fryefryefrye/Open-Source-RKS/OtherProject/clock/1.jpg

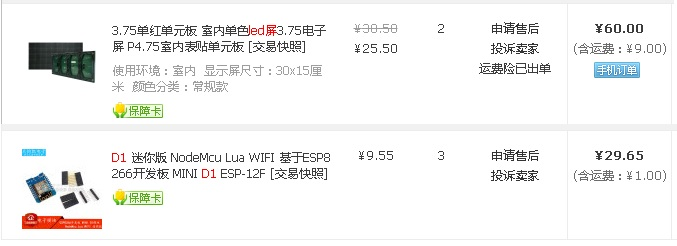
OtherProject/clock/1.jpg
