fryefryefrye/Open-Source-RKS/OtherProject/clock/2.jpg

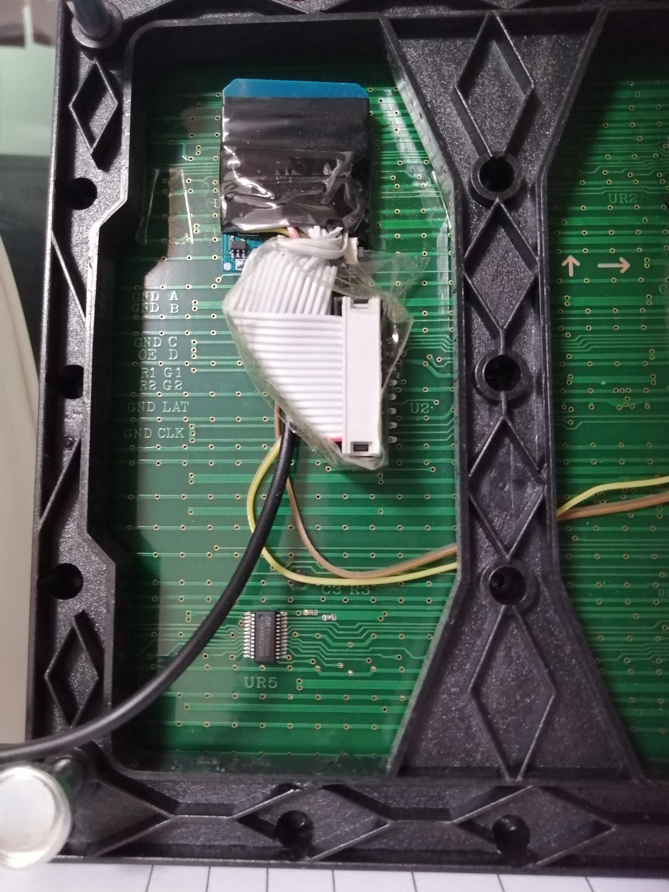
OtherProject/clock/2.jpg
