fryefryefrye/Open-Source-RKS/OtherProject/clock/3.jpg

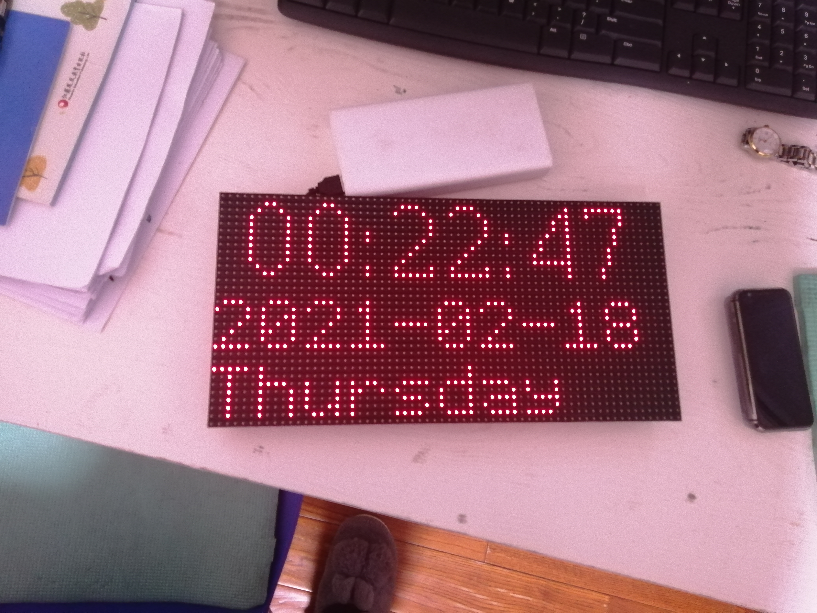
OtherProject/clock/3.jpg
