fryefryefrye/Open-Source-RKS/OtherProject/clock/4.jpg

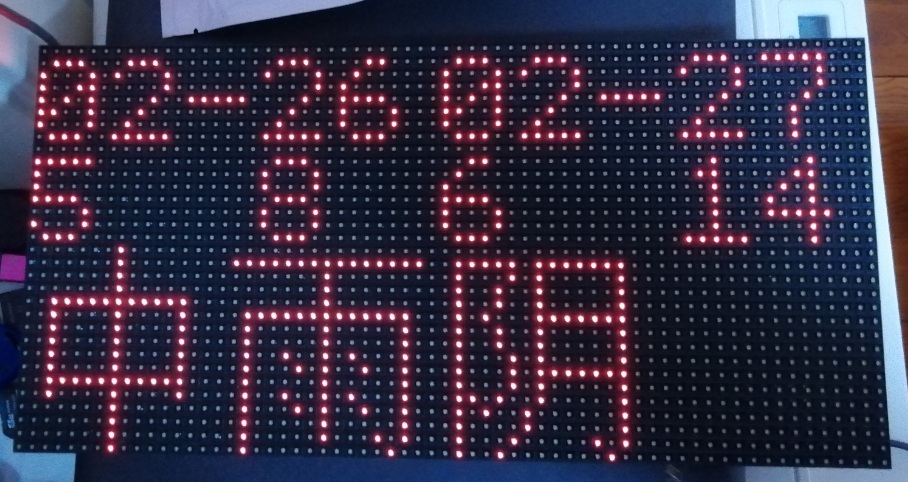
OtherProject/clock/4.jpg
