fryefryefrye/Open-Source-RKS/OtherProject/clock/IMG_20210221_115505.jpg

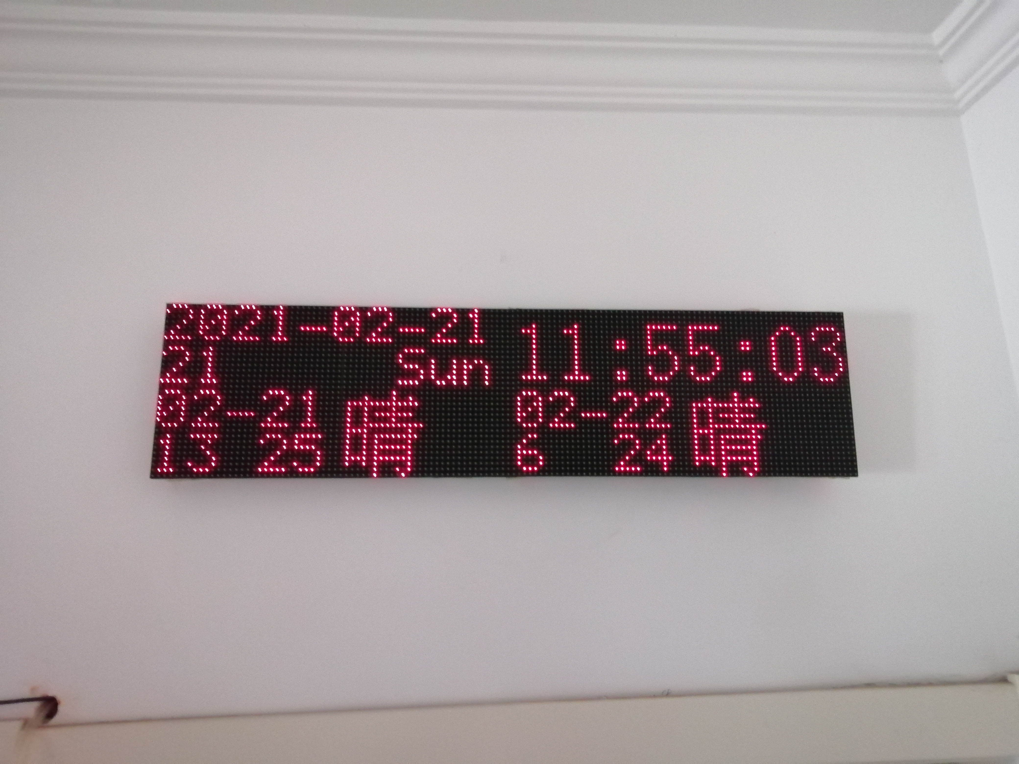
OtherProject/clock/IMG_20210221_115505.jpg
