fryefryefrye/Open-Source-RKS/OtherProject/HomeAutomation/1.jpg

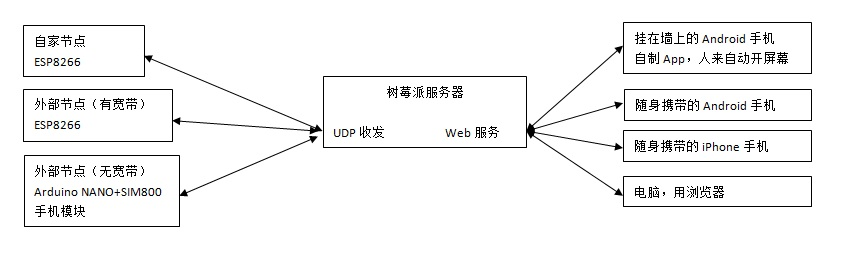
OtherProject/HomeAutomation/1.jpg
