fryefryefrye/Open-Source-RKS/OtherProject/HomeAutomation/2.jpg

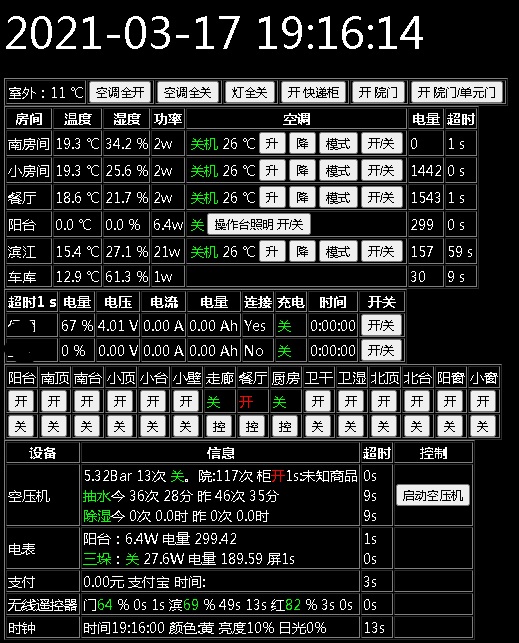
OtherProject/HomeAutomation/2.jpg
