fryefryefrye/Open-Source-RKS/Tag/ble/hal/nordic_common.h

/* Copyright (c) 2009 Nordic Semiconductor. All Rights Reserved.
 *
 * The information contained herein is confidential property of Nordic 
 * Semiconductor ASA.Terms and conditions of usage are described in detail 
 * in NORDIC SEMICONDUCTOR STANDARD SOFTWARE LICENSE AGREEMENT. 
 *
 * Licensees are granted free, non-transferable use of the information. NO
 * WARRENTY of ANY KIND is provided. This heading must NOT be removed from
 * the file.
 *              
 * $LastChangedRevision: 2513 $
 */

/** @file
 * @brief Common defines and macros for firmware developed by Nordic Semiconductor.
 *
 */

#ifndef NORDIC_COMMON_H__
#define NORDIC_COMMON_H__

/** Swaps the upper byte with the lower byte in a 16 bit variable */
//lint -emacro((572),SWAP) // Suppress warning 572 "Excessive shift value"
#define SWAP(x) ((((x)&0xFFU)<<8)|(((x)>>8)&0xFFU))

/** The upper 8 bits of a 16 bit value */
#define MSB(a) (((a) & 0xFF00U) >> 8)
/** The lower 8 bits (of a 16 bit value) */
#define LSB(a) (((a) & 0xFFU))

/** Leaves the minimum of the two arguments */
#define MIN(a, b) ((a) < (b) ? (a) : (b))
/** Leaves the maximum of the two arguments */
#define MAX(a, b) ((a) < (b) ? (b) : (a))

#define BIT_0 0x01U /**< The value of bit 0 */
#define BIT_1 0x02U /**< The value of bit 1 */
#define BIT_2 0x04U /**< The value of bit 2 */
#define BIT_3 0x08U /**< The value of bit 3 */
#define BIT_4 0x10U /**< The value of bit 4 */
#define BIT_5 0x20U /**< The value of bit 5 */
#define BIT_6 0x40U /**< The value of bit 6 */
#define BIT_7 0x80U /**< The value of bit 7 */
#define BIT_8 0x0100U /**< The value of bit 8 */
#define BIT_9 0x0200U /**< The value of bit 9 */
#define BIT_10 0x0400U /**< The value of bit 10 */
#define BIT_11 0x0800U /**< The value of bit 11 */
#define BIT_12 0x1000U /**< The value of bit 12 */
#define BIT_13 0x2000U /**< The value of bit 13 */
#define BIT_14 0x4000U /**< The value of bit 14 */
#define BIT_15 0x8000U /**< The value of bit 15 */


#endif // NORDIC_COMMON_H__
